REPALphilread/ReP_AL-3D-Lawn-Mower/Mower Arduino Code/Mower_V7.0/Readme.txt

ReP_AL 3D Printed Robot Lawn Mower
----------------------------------

Code V7.0
------------------------------

Upload the MEGA code to the Arduino MEGA
Upload the Nano code to the Arduino Nano
Upload the NodeMCU code to the NodeMCU Board   (includes new code)

Features of 7.0
---------------

- Nearly all of the major Mower settings can now be set using the LCD screen and keypad
- Settings are saved to EEPROM so they are transfered to later code updates.
- Setting Alarms has been improved with an action available for each alarm.
- Fixed the hours and minutes roll over in the alarm setting.
- Fixed errorsa with exiting the settings sub menu.

NodeMCU Board URL:
------------------
Use this URL to add the NodeMCU board 1.0 to the boards menu.

http://arduino.esp8266.com/stable/package_esp8266com_index.json
