REPALphilread/ReP_AL-3D-Lawn-Mower/Mower Arduino Code/Mower_V6.8/Readme.txt

ReP_AL 3D Printed Robot Lawn Mower
----------------------------------

Code V6.8
------------------------------

Upload the MEGA code to the Arduino MEGA
Upload the Nano code to the Arduino Nano
Upload the NodeMCU code to the NodeMCU Board   (includes new code)

Features of 6.8
---------------

- Fixed error in Clock Setting
- Improved the reliability of Compass Home
- Added a test menu to Go Home to test the docking procedure.

NodeMCU Board URL:
http://arduino.esp8266.com/stable/package_esp8266com_index.json
