REPALphilread/ReP_AL-3D-Lawn-Mower/Mower Arduino Code/Mower_V6.6/Readme.txt

ReP_AL 3D Printed Robot Lawn Mower
----------------------------------

Code V6.4
------------------------------

Upload the MEGA code to the Arduino MEGA
Upload the Nano code to the Arduino Nano
Upload the NodeMCU code to the NodeMCU Board

Features of 6.6
---------------

- Spiral cut feature available.  (be careful on slopes)
- More EEPROM settings available
- Improved compass home feature and angle setting

DO NOT USE!!!!

- Tip safety - not working yet
- Parallel cut - not working 100% yet.

NodeMCU Board URL:
http://arduino.esp8266.com/stable/package_esp8266com_index.json
