REPALphilread/ReP_AL-3D-Lawn-Mower/Mower Arduino Code/Mower_V6.2/Readme.txt

ReP_AL 3D Printed Robot Lawn Mower
----------------------------------

Code V6.2   
------------------------------

Upload the MEGA code to the Arduino MEGA
Upload the Nano code to the Arduino Nano (same as 6.1)
Upload the NodeMCU code to the NodeMCU Board (same as 6.1)

Features of 6.2
---------------

- Alarm timer function fixed
- Added more options for timed mow
- Easier menu in code to add custom options
- mower displays the off time in timed mow.

NodeMCU Board URL:
http://arduino.esp8266.com/stable/package_esp8266com_index.json
