REPALphilread/ReP_AL-3D-Lawn-Mower/Mower Arduino Code/Mower_V6.10/Readme.txt

ReP_AL 3D Printed Robot Lawn Mower
----------------------------------

Code V6.1   
------------------------------

Upload the MEGA code to the Arduino MEGA
Upload the Nano code to the Arduino Nano
Upload the NodeMCU code to the NodeMCU Board

Features of 6.1
---------------

- Menu options have been improved. Scrolling in both directions and easier coding.
- More Test options have been added including a compass test and a volt amps test
- First trials at compass mowing (very initial stages - not working well and not advised to use it yet)
- Stabilised the heading hold by using compass degrees instead of heading.

NodeMCU Board URL:
http://arduino.esp8266.com/stable/package_esp8266com_index.json
