REPALphilread/ReP_AL-3D-Lawn-Mower/Mower Arduino Code/Mower_V5.3.2/Readme.txt

ReP_AL 3D Printed Robot Lawn Mower
----------------------------------

Code V5.3.2    - BETA (in  test)
------------------------------

Upload the MEGA code to the Arduino MEGA
Upload the Nano code to the Arduino Nano

Features of 5.2
---------------

- BETA for tracking to home (please test)
  All the charge detection has been moved to the Nano
  Enter the Nano amp limits in the NANO code for your charger to send a charge = 1 signal to the MEGA when the charger is detected.
- Improved the Serial output visual for easier overview of what the mower is doing.
