REPALphilread/ReP_AL-3D-Lawn-Mower/Mower Arduino Code/Mower_V5.8/Readme.txt

ReP_AL 3D Printed Robot Lawn Mower
----------------------------------

Code V5.8    - BETA 
------------------------------

Upload the MEGA code to the Arduino MEGA
Upload the Nano code to the Arduino Nano

Features of 5.8
---------------

- Code layout and logic is changed - I needed to simplify it all to make the WIFI possible in the future
- Test sketches intgrated into the main program.  Choose Tests on the menu options and select the test
- Rain sensor added - turn on and off in the settings
- Improved Serial communication between the NANO and the MEGA.
- Reverse motors option removed. You need to get the cables correct. Its too complicasted to cater for all cabling variations
-
