REPALphilread/ReP_AL-3D-Lawn-Mower/Mower Arduino Code/Mower_V9.2/SDCard BMP/PID.bmp

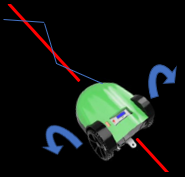
Mower Arduino Code/Mower_V9.2/SDCard BMP/PID.bmp
