REPALphilread/ReP_AL-3D-Lawn-Mower/Metal Parts/STL/Rear Axle - Little Monster.stl

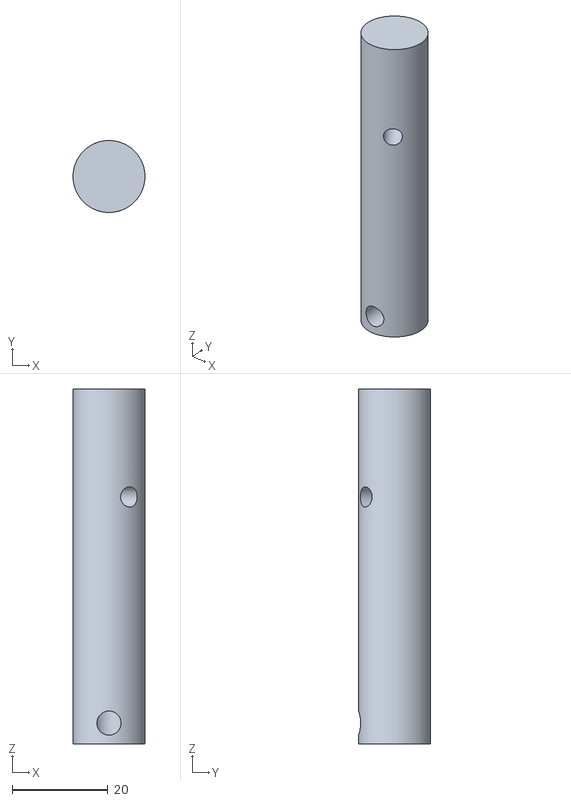
[picture p24: CAD file, 2020-04-30, last stored version]
Metal Parts/STL/Rear Axle - Little Monster.stl
15.0 x 15.0 x 74.0
