REPALphilread/ReP_AL-3D-Lawn-Mower/RTK GPS STL Files/STL RTK Base Station Case/02 Sliding Lid.stl

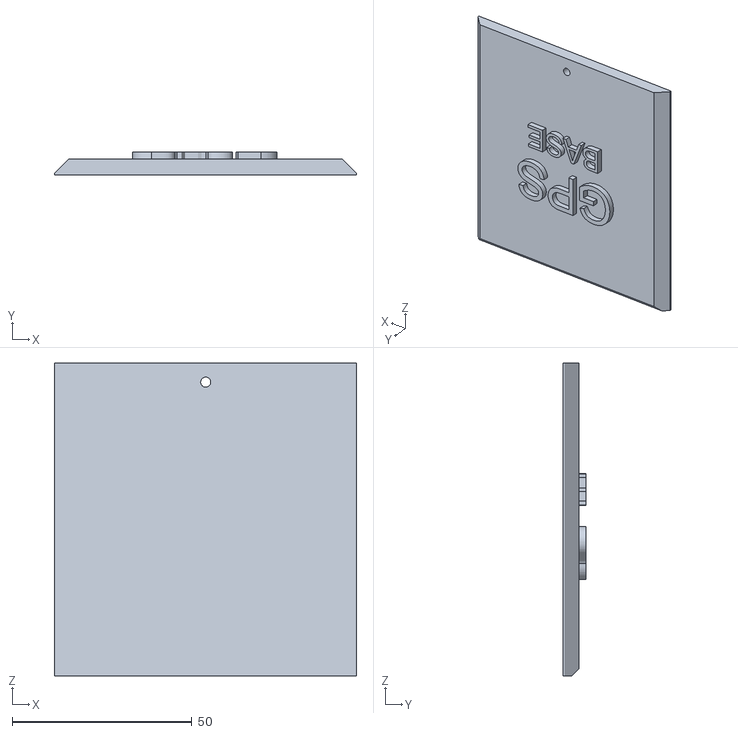
[picture p25: CAD file, 2020-06-30, last stored version]
RTK GPS STL Files/STL RTK Base Station Case/02 Sliding Lid.stl
84.0 x 6.50 x 86.9
