REPALphilread/ReP_AL-3D-Lawn-Mower/RTK GPS STL Files/STL RTK GPS Rover Case/ESP32 Lid.stl

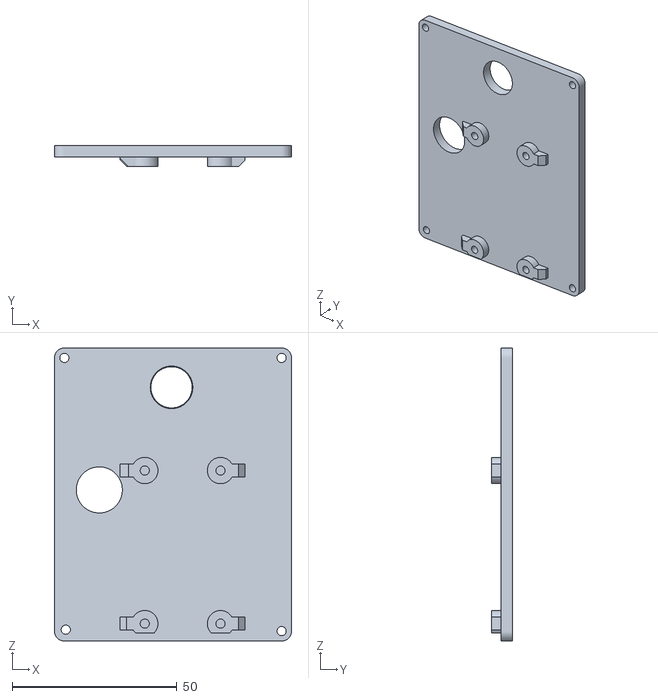
[picture p26: CAD file, 2020-06-30, last stored version]
RTK GPS STL Files/STL RTK GPS Rover Case/ESP32 Lid.stl
72.0 x 6.48 x 89.0
