REPALphilread/ReP_AL-3D-Lawn-Mower/Metal Parts Step Files/Drill Templates/Blade Motor Adapter/Hand Drill/02 Blade Adapter Hand Drill 2.stl

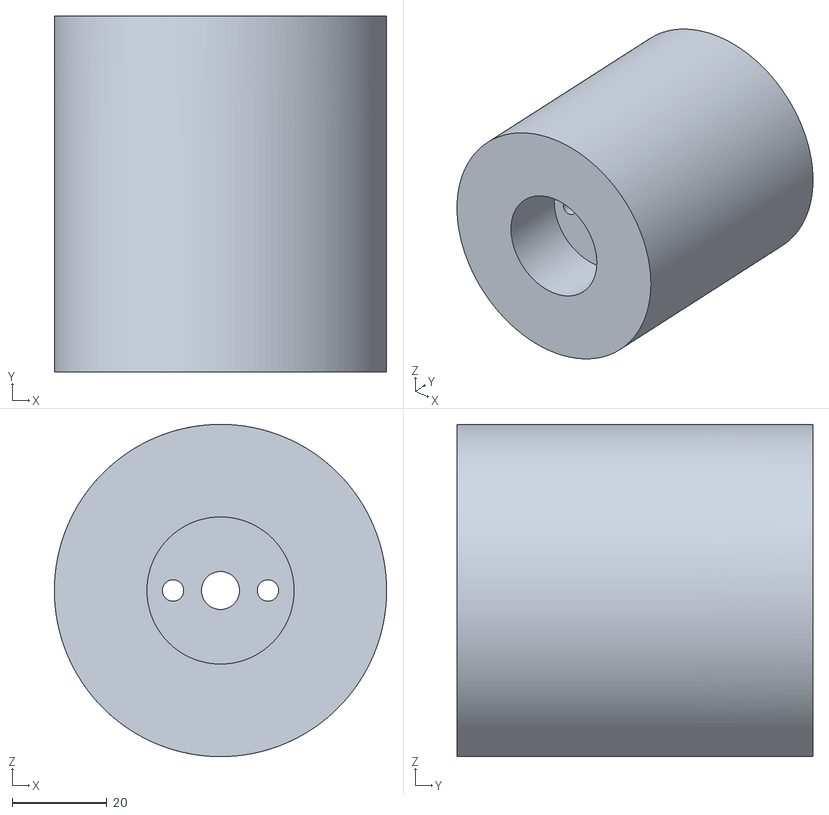
[picture p27: CAD file, 2020-04-07, last stored version]
Metal Parts Step Files/Drill Templates/Blade Motor Adapter/Hand Drill/02 Blade Adapter Hand Drill 2.stl
70.0 x 75.0 x 70.0
