REPALphilread/ReP_AL-3D-Lawn-Mower/Metal Parts Step Files/Drill Templates/Wheel Axle/Drill Press/01 Drill 3mm End Hole Template.stl

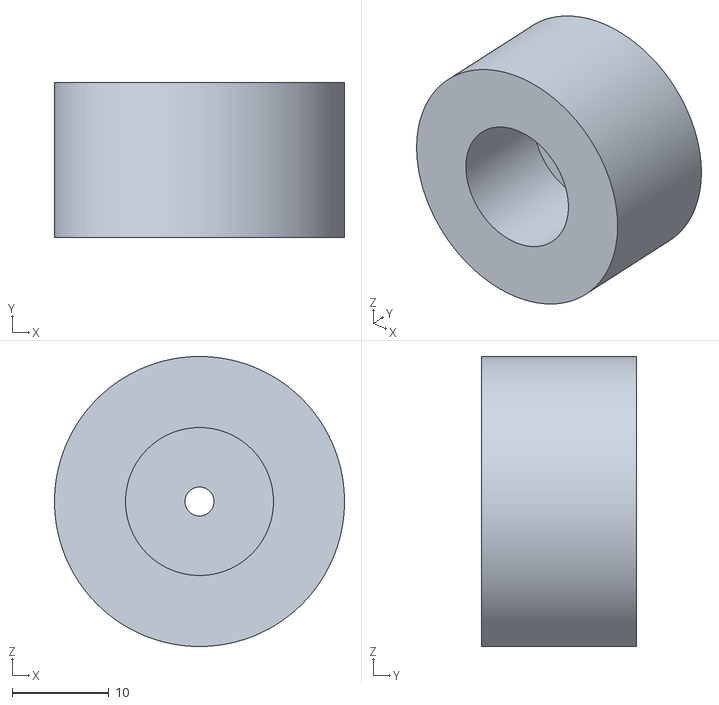
[picture p28: CAD file, 2020-04-07, last stored version]
Metal Parts Step Files/Drill Templates/Wheel Axle/Drill Press/01 Drill 3mm End Hole Template.stl
30.0 x 16.0 x 30.0
