REPALphilread/ReP_AL-3D-Lawn-Mower/Metal Parts Step Files/Drill Templates/Wheel Axle/Hand Drill/02 Drill 6mm End Hole Hand Drill Template.stl

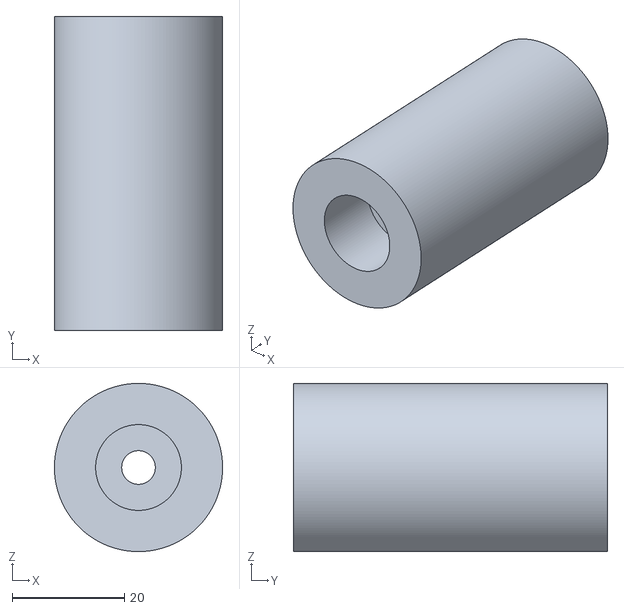
[picture p29: CAD file, 2020-04-07, last stored version]
Metal Parts Step Files/Drill Templates/Wheel Axle/Hand Drill/02 Drill 6mm End Hole Hand Drill Template.stl
30.0 x 56.0 x 30.0
