REPALphilread/ReP_AL-3D-Lawn-Mower/Metal Parts/STL/Mower Disc Adapter.stl

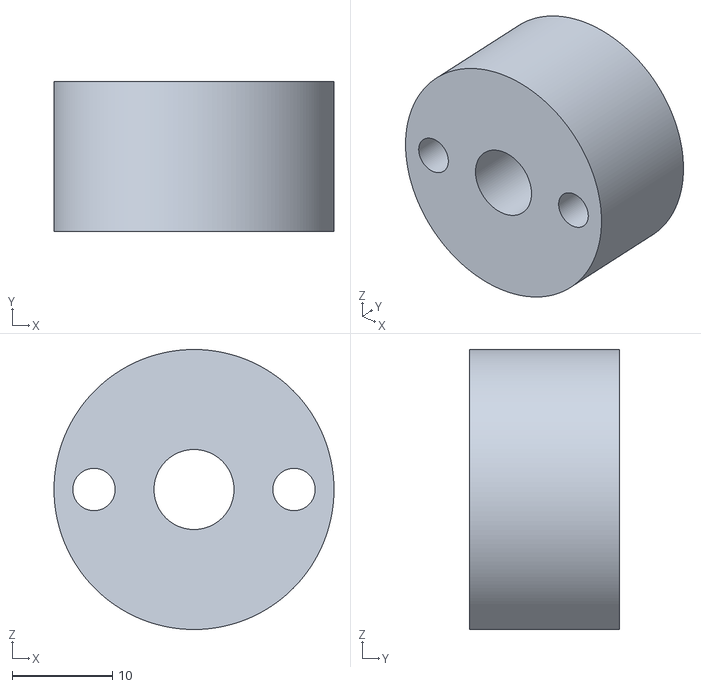
[picture p30: CAD file, 2020-04-30, last stored version]
Metal Parts/STL/Mower Disc Adapter.stl
28.0 x 15.0 x 28.0
