REPALphilread/ReP_AL-3D-Lawn-Mower/RTK GPS STL Files/STL RTK Base Station Case/03 Wire Clamp.stl

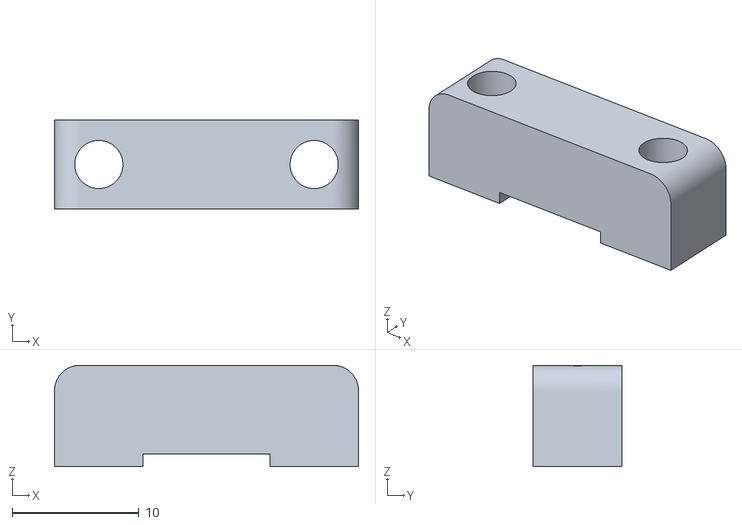
[picture p31: CAD file, 2020-06-30, last stored version]
RTK GPS STL Files/STL RTK Base Station Case/03 Wire Clamp.stl
24.0 x 7.00 x 8.00
