REPALphilread/ReP_AL-3D-Lawn-Mower/Metal Parts/STL/Rear Axle - 330 LAM.stl

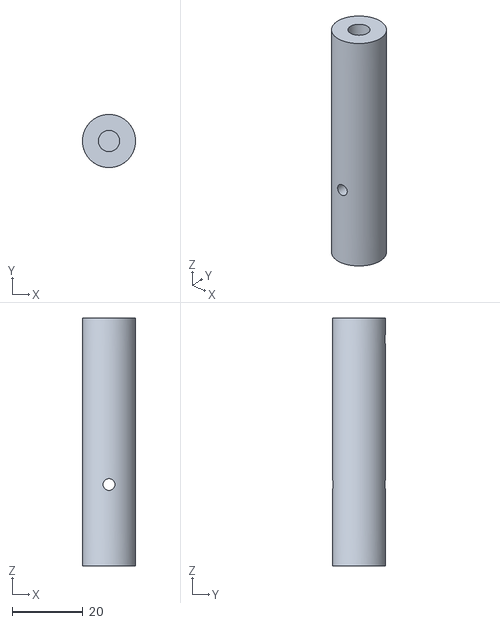
[picture p32: CAD file, 2020-04-30, last stored version]
Metal Parts/STL/Rear Axle - 330 LAM.stl
15.0 x 15.0 x 70.0
