REPALphilread/ReP_AL-3D-Lawn-Mower/Metal Parts Step Files/Drill Templates/95 Drill 5.5mm End Template.stl

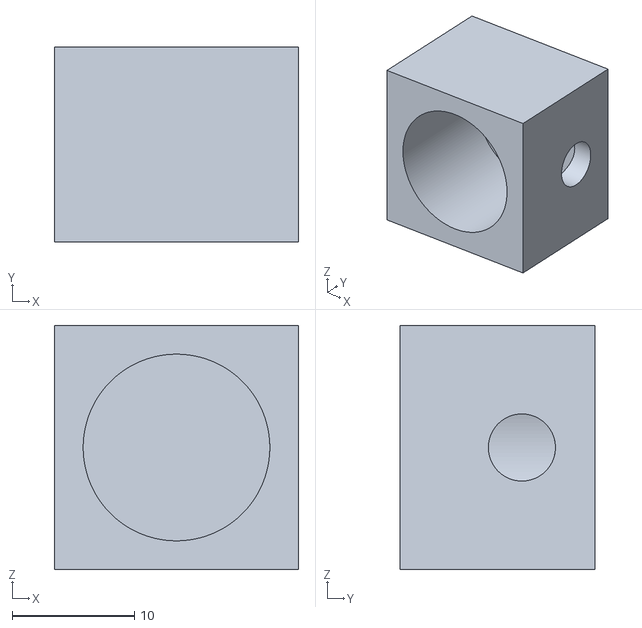
[picture p33: CAD file, 2020-04-07, last stored version]
Metal Parts Step Files/Drill Templates/95 Drill 5.5mm End Template.stl
20.0 x 16.0 x 20.0
