REPALphilread/ReP_AL-3D-Lawn-Mower/Perimeter Wire Transmitter/Sender_Station_V2.ino

/*
  Ardumower (www.ardumower.de)
 Copyright (c) 2013-2014 by Alexander Grau
 Copyright (c) 2013-2014 by Sven Gennat
 Copyright (c) 2015 by Jürgen Lange
 
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
 You should have received a copy of the GNU General Public License
 along with this program.  If not, see <http://www.gnu.org/licenses/>.
 */

/*
  Perimeter sender v2   (for details see   http://wiki.ardumower.de/index.php?title=Perimeter_wire  )  
 Requires: Perimeter sender PCB v1.0   ( https://www.marotronics.de/Perimeter-Sender-Prototyp )
 
 */

#include <EEPROM.h>
#include <RunningMedian.h>
#include <TimerOne.h>




//#define USE_DEVELOPER_TEST    1      // uncomment for new perimeter signal test (developers) 
//---------------------------------------------------------------------------------------------------

#define USE_AUTO_PERIMETER_CURRENT  1 // Use auto Perimeter power set to 0 for not used
// Spannungsmessung
long previousMillisVolt = 0;        // will store last time messure was updated
long intervalVolt = 5;           // voltage messeurement interval (milliseconds)
int counterVolt = 0; // messurement counter for output voltage
int VoltAdc = 0 ; // actual ADC voltage messurement
float Vref = 5.0; // reference Voltage of ADC
float R1 = 100000.0; //value of voltage divider resistor (R1)
float R2 = 10000.0; //value of voltage divider resistor (R2)
float Vdc = 0; // actual messurement voltage in Volt
// Strommessung
long previousMillisAmpere = 0; //Perimeter current last messeurement
long intervalAmpere = 10; // Perimeter current messeurement interval (milliseconds)
int counterAmpere = 0; // messurement counter for Perimeter current average 
float AmpereAdc = 0; // actual ADC messurement for Perimeter current
float AmpereDC = 0; // actual Perimeter current in Ampere
// Leistung
float perimeterPower = 0; // actual Perimeter power in watts
float perimeterMaxPower = 7.00; // (7W) Max Perimeter transmitting power in watts
byte perimeterPowerPWM = 200; // PWM start value
#define pinPerimeterPower  11 // PWM pin for Voltage-Control (11)--->(OPA2340)--->(PIN 4 of LM2596)

byte printTag = 1;                    // Ausgabesteuerung c = calib, 0 = normal, 1 = Regelung
// --- MC33926 motor driver ---
#define USE_DOUBLE_AMPLTIUDE    1         // uncomment to use +/- input voltage for amplitude (default), 
// comment to use only +input/GND voltage for amplitude

#define pinIN1       9  // M1_IN1         (if using old L298N driver, connect this pin to L298N-IN1)
#define pinIN2       2  // M1_IN2         (if using old L298N driver, connect this pin to L298N-IN2)
#define pinPWM       3  // M1_PWM / nD2   (if using old L298N driver, leave open)
#define pinEnable    5  // EN             (connect to motor driver enable)             

// motor driver fault pin
#define pinFault     4  // M1_nSF
#define USE_PERI_FAULT        0     // use pinFault for driver fault detection? (set to '0' if not connected!)

// motor driver feedback pin (=perimeter open/close detection, used for status LED)
#define USE_PERI_CURRENT      0     // use pinFeedback for perimeter current measurements? (set to '0' if not connected!)
#define pinFeedback A0  // M1_FB
#define PERI_CURRENT_MIN    0.03     // minimum Ampere for perimeter-is-closed detection 

// ---- sender current control (via potentiometer) ----
// sender modulates signal (PWM), based on duty-cycle set via this potentiometer
#define USE_POT      0  // use potentiometer for current control? (set to '0' if not connected!)
#define pinPot      A3  // 100k potentiometer (current control)   

// ---- sender automatic standby (via current sensor for charger) ----
// sender detects robot via a charging current through the charging pins
#define USE_CHG_CURRENT       0     // use charging current sensor for robot detection? (set to '0' if not connected!)
#define pinChargeCurrent     A2     // ACS712-05 current sensor OUT
#define CHG_CURRENT_MIN   0.008      // minimum Ampere for charging detection

// ---- sender status LED ----
#define  pinLED 13  // ON: perimeter closed, OFF: perimeter open, BLINK: robot is charging


// code version 
#define VER "592"

// --------------------------------------

volatile int step = 0;
volatile boolean enableSender = true;


double duty = 1.0;    // 100 duty%
int dutyPWM = 0;
double chargeCurrent = 0;
double periCurrentAvg = 0; 
double periCurrentMax = 0; 
int faults = 0;
boolean isCharging = false;
boolean stateLED = false;
unsigned int chargeADCZero = 0;
RunningMedian<unsigned int,16> periCurrentMeasurements;
RunningMedian<unsigned int,96> chargeCurrentMeasurements;

unsigned long nextTimeControl = 0;
unsigned long nextTimeInfo = 0;
unsigned long nextTimeToggleLED = 0;


// must be multiple of 2 !
// http://grauonline.de/alexwww/ardumower/filter/filter.html    
// "pseudonoise4_pw" signal (sender)

#ifdef USE_DEVELOPER_TEST
// a more motor driver friendly signal (sender)
int8_t sigcode[] = {  
  1,0,0,0,0,
  1,0,0,0,0,
  -1,0,0,0,0,
  1,0,0,0,0   };
#else
int8_t sigcode[] = { 
  1,1,-1,-1,1,-1,1,-1,-1,1,-1,1,1,-1,-1,1,-1,-1,1,-1,-1,1,1,-1 };
#endif


// using transparently 5v / 1.1v ref
int analogReadMillivolt(int pin){
  int millivolt;
  int adc;
  // first read using 5v ref 
  adc = analogRead(pin);
  millivolt = ((double)adc) / 1024.0 * 5000.0;  
  // ist so nicht sinnvoll da der ADC Zeit braucht sich umzustellen erste Messung ist ungenau!!
  /* if (adc < 10){
   // read using 1.1v ref
   analogReference(INTERNAL);
   adc = analogRead(pin);
   millivolt = ((double)adc) / 1024.0 * 1100.0;
   analogReference(DEFAULT); 
   }*/
  return millivolt;
}


void timerCallback(){       
  if (enableSender){
    if (sigcode[step] == 1) {      
      digitalWrite(pinIN1, LOW);                           
#ifdef USE_DOUBLE_AMPLTIUDE      
      digitalWrite(pinIN2, HIGH);                                 
#endif             
      digitalWrite(pinEnable, HIGH);
    } 
    else if (sigcode[step] == -1) {              
      digitalWrite(pinIN1, HIGH);          
      digitalWrite(pinIN2, LOW);                                 
      digitalWrite(pinEnable, HIGH);                           
    } 
    else {
      digitalWrite(pinEnable, LOW);
    } 
    step ++;    
    if (step == sizeof sigcode) {      
      step = 0;      
    }    
  } 
  else {
    digitalWrite(pinEnable, LOW);    
  }
}

void readEEPROM(){
  if (EEPROM.read(0) == 43){
    // EEPROM data available
    chargeADCZero = (EEPROM.read(1) << 8) | EEPROM.read(2);
  } 
  else Serial.println("no EEPROM data found, using default calibration (INA169)");
  Serial.print("chargeADCZero=");
  Serial.println(chargeADCZero);  
}


void calibrateChargeCurrentSensor(){
  Serial.println("calibrateChargeCurrentSensor (note: robot must be outside charging station!)");
  RunningMedian<unsigned int,32> measurements;
  for (unsigned int i=0; i < measurements.getSize(); i++) {
    unsigned int m = analogRead(pinChargeCurrent);
    //Serial.println(m);
    measurements.add( m );
    delay(50);
  }
  float v;
  measurements.getAverage(v);  
  chargeADCZero = v;
  EEPROM.write(0, 43);
  EEPROM.write(1, chargeADCZero >> 8);
  EEPROM.write(2, chargeADCZero & 255);  
  Serial.println("calibration done");
  readEEPROM();
} 



void setup() {  
  pinMode(pinIN1, OUTPUT);    
  pinMode(pinIN2, OUTPUT);  
  pinMode(pinEnable, OUTPUT);
  pinMode(pinPWM, OUTPUT);  
  pinMode(pinFeedback, INPUT);    
  pinMode(pinFault, INPUT);      
  pinMode(pinPot, INPUT);      
  pinMode(pinChargeCurrent, INPUT);
  analogWrite(pinPerimeterPower, perimeterPowerPWM);
  // configure ADC reference
  analogReference(DEFAULT); // ADC 5.0v ref    
  //analogReference(INTERNAL); // ADC 1.1v ref       

  // sample rate 9615 Hz (19230,76923076923 / 2 => 9615.38)
  int T = 1000.0*1000.0/ 9615.38;
  Serial.begin(115200);

  Serial.println("START");
  Serial.print("Ardumower Sender ");
  Serial.println(VER);
#ifdef USE_DEVELOPER_TEST
  Serial.println("Warning: USE_DEVELOPER_TEST activated");
#endif
  //Serial.println("press...");
  //Serial.println("  1  for current sensor calibration");  
  //Serial.println();

  readEEPROM();
  Serial.print("T=");
  Serial.println(T);    
  Serial.print("f=");
  Serial.println(1000.0*1000.0/T);    
  Timer1.initialize(T);         // initialize timer1, and set period
  //Timer1.pwm(pinPWM, 256);  
  Timer1.attachInterrupt(timerCallback);  
  //digitalWrite(pinIN1, HIGH);
  //digitalWrite(pinIN2, LOW);  
  //tone(pinPWM, 7800);

  // http://playground.arduino.cc/Main/TimerPWMCheatsheet
  // timer 2 pwm freq 31 khz  
  //cli();
  TCCR2B = TCCR2B & 0b11111000 | 0x01;
  //TIMSK2 |= (1 << OCIE2A);     // Enable Output Compare Match A Interrupt  
  //OCR2A = 255;                 // Set compared value
  //sei();
}

void checkKey(){
  if (Serial.available() > 0) {
    char ch = (char)Serial.read();            
    Serial.print("received key=");
    Serial.println(ch);
    while (Serial.available()) Serial.read();
    switch (ch){
    case 'c': 
      calibrateChargeCurrentSensor();           
      break;
    case '0': 
      printTag = 0;           
      break;
    case '1': 
      printTag = 1;           
      break;
    }
  }             
}

// Interrupt service run when Timer/Counter2 reaches OCR2A
//ISR(TIMER2_COMPA_vect) {
//  if (digitalRead(pinFault) == LOW) fault = true; 
//if (digitalRead(pinPWM) == HIGH) fault = true; 
//fault = true;

void fault(){
  Serial.println("MC_FAULT");
  for (int i=0; i < 10; i++){
    digitalWrite(pinLED, HIGH);
    delay(50);
    digitalWrite(pinLED, LOW);
    delay(50);
  }  
  faults++;                          
}


void loop()
{
  //---------------------------------------------------------------------------------------------------
  if(USE_AUTO_PERIMETER_CURRENT)
  {
    unsigned long currentMillis = millis(); // save actual moment

    // -----------------------------------------------------------------------------------------
    //                   Messurement of Voltage and Calculate Perimeter-Power
    // -----------------------------------------------------------------------------------------
    if(currentMillis - previousMillisVolt > intervalVolt) // check messurement interval
    {
      previousMillisVolt = currentMillis; // save the last time of messurement  

      if (counterVolt < 49) // check average messurement Volt-counter
      {
        counterVolt ++; // add counter +1
        VoltAdc = VoltAdc + analogRead(A3); // add actual messurement to previous messurement
      } 
      else 
      {
        VoltAdc = VoltAdc / 50; // calculate average voltage
        Vdc = (VoltAdc*5.0)/1024; // calculate real voltage
        Vdc=(Vdc*((R1+R2)/R2))+0.3; // (+0.3) = correction factor over all
        perimeterPower = Vdc * AmpereDC; // calculate Perimeter-Power
        counterVolt = 0; // set counter to 0 for next messurement
        // **** Control Perimeter-Power adjust DC/DC converter voltage over PWM ****
        // step output voltage down
        if(perimeterPower > perimeterMaxPower && perimeterPowerPWM < 255) perimeterPowerPWM ++;
        // step output voltage up
        if(perimeterPower < perimeterMaxPower && perimeterPowerPWM > 1) perimeterPowerPWM --;
        analogWrite(pinPerimeterPower, perimeterPowerPWM); // set new PWM value for output
      }
    }
    // -----------------------------------------------------------------------------------------
    //                          Messurement of Current for Perimeter-Power
    // -----------------------------------------------------------------------------------------
    if(currentMillis - previousMillisAmpere > intervalAmpere) // check messurement interval 
    {
      previousMillisAmpere = currentMillis; // save the last time of messurement   

      if (counterAmpere < 19) // check average messurement Current-counter
      {
        counterAmpere ++; // add counter +1
        AmpereAdc = AmpereAdc + analogRead(A7); // add actual messurement to previous messurement
      } 
      else 
      {
        AmpereAdc = AmpereAdc / 20; // calculate average current
        AmpereDC = AmpereAdc*Vref/1023*0.5; // calculate real current
        counterAmpere = 0;  // set counter to 0 for next messurement
      }
    }
    // -----------------------------------------------------------------------------------------
    // -----------------------------------------------------------------------------------------
  } // <------------- END if(USE_AUTO_PERIMETER_CURRENT)
  // -------------------------------------------------------------------------------------------
  // -------------------------------------------------------------------------------------------
  // -------------------------------------------------------------------------------------------
  if (millis() >= nextTimeControl){                    
    nextTimeControl = millis() + 100;
    dutyPWM = ((int)(duty * 255.0));
    if (isCharging){
      // switch off perimeter 
      enableSender = false;
    } 
    else {
      // switch on perimeter
      enableSender = true;
      //analogWrite(pinPWM, 255);
      analogWrite(pinPWM, dutyPWM);
      if ( USE_PERI_FAULT && (dutyPWM == 255) && (digitalRead(pinFault) == LOW) ) {
        enableSender = false;
        dutyPWM = 0;
        analogWrite(pinPWM, dutyPWM);
        fault();    
      }    
    }
  }

  if (millis() >= nextTimeInfo){                
    nextTimeInfo = millis() + 500;                
    checkKey();        

    //unsigned int v = 0;
    float v = 0;
    // determine charging current (Ampere)        
    if (USE_CHG_CURRENT) {                
      chargeCurrentMeasurements.getAverage(v);        
      chargeCurrent = ((double)(((int)v)  - ((int)chargeADCZero))) / 1023.0 * 1.1;  
      isCharging = (abs(chargeCurrent) >= CHG_CURRENT_MIN); 
    }  

    if (USE_PERI_CURRENT) {
      // determine perimeter current (Ampere)
      periCurrentMeasurements.getAverage(v);    
      periCurrentAvg = ((double)v) / 1023.0 * 1.1 / 0.525;   // 525 mV per amp    
      unsigned int h;
      periCurrentMeasurements.getHighest(h);    
      periCurrentMax = ((double)h) / 1023.0 * 1.1 / 0.525;   // 525 mV per amp    
    }

    if(printTag == 0)
    {
      Serial.print("time=");
      Serial.print(millis()/1000);    
      Serial.print("\tchgCurrent=");
      Serial.print(chargeCurrent, 3);
      Serial.print("\tchgCurrentADC=");
      chargeCurrentMeasurements.getAverage(v);        
      Serial.print( v );       
      Serial.print("\tisCharging=");
      Serial.print(isCharging);    
      Serial.print("\tperiCurrent avg=");
      Serial.print(periCurrentAvg);
      Serial.print("\tmax=");
      Serial.print(periCurrentMax);
      Serial.print("\tduty=");
      Serial.print(duty);
      Serial.print("\tdutyPWM=");        
      Serial.print(dutyPWM);        
      Serial.print("\tfaults=");
      Serial.print(faults);       
      Serial.println();
    }

    if(printTag == 1)
    {
      Serial.print("V-OUT= ");
      Serial.print(Vdc);    
      Serial.print("  A-OUT= ");
      Serial.print(AmpereDC, 2);
      Serial.print("  P-OUT-MAX= ");
      Serial.print(perimeterMaxPower);
      Serial.print("  P-OUT= ");
      Serial.print(perimeterPower, 2);
      Serial.print("  PWM-OUT= ");
      Serial.print(perimeterPowerPWM);
      Serial.println();
    }

    if (USE_POT){
      // read potentiometer
      duty = max(0.01, ((float)map(analogRead(pinPot),  0,1023,   0,1000))  /1000.0 );
    }              
  }

  if (USE_PERI_CURRENT) {
    periCurrentMeasurements.add( analogRead(pinFeedback) );    
  }

  if (USE_CHG_CURRENT){
    // determine charging current (Ampere)         
    chargeCurrentMeasurements.add( analogRead( pinChargeCurrent) );
  }

  // LED status 
  if (isCharging) {    
    // charging
    if (millis() >= nextTimeToggleLED){
      nextTimeToggleLED = millis() + 500;
      stateLED = !stateLED;
    }
  } 
  else {
    // not charging => indicate perimeter wire state (OFF=broken)
    stateLED = (periCurrentAvg >= PERI_CURRENT_MIN);
  }
  digitalWrite(pinLED, stateLED);   


}
