REPALphilread/ReP_AL-3D-Lawn-Mower/Mower Arduino Code/Mower_V9.2/NODEMCU_V9.2/NODEMCU_V9.2.ino

/* Comment this out to disable prints and save space */
#define BLYNK_PRINT Serial
#include <ESP8266WiFi.h>
#include <BlynkSimpleEsp8266.h>
#include <SoftwareSerial.h>

SoftwareSerial NodeMCU(D2,D3);   //RXD2 TXD3

//#define LED LED_BUILTIN

#define LED D4      // on various NODEMCU boards the LED Pin is different.....

// You should get Auth Token in the Blynk App.
// Go to the Project Settings (nut icon).

char auth[] = "Blynk Token Number";


// Your WiFi credentials.
// Set password to "" for open networks.
char ssid[] = "WIFI NAME";
char pass[] = "WIFI Password";


int buttonState = 0;
char  Version[16];

// RX Variables
float val_VoltNow;                  // Battery Voltage from MEGA
float BatteryVoltage;               // Voltage read last RX
int Loop_Cycle_Mowing;              // Current Loop Cycle from MEGA

int Mower_Parked;
int Mower_Parked_Low_Batt;
int Mower_Docked;
int Mower_Docked_Filter;
int Mower_Running;
int Mower_Running_Filter;
int Mower_Lost;
int Charge_Detected;
int Tracking_Wire;
int Compass_Heading_Lock;

int Compass_Activate;
int Compass_Heading_Hold_Enabled;
int GYRO_Enabled;

int Sonar_1_Activate;
int Sonar_2_Activate;
int Sonar_3_Activate;
int Bumper_Activate_Frnt;

int i;                              // Transmit blank code

bool Mower_Already_Started = 0;
bool Going_Home_Already = 0;

int j;
int k;
int transmit_blynk_code = 0;

bool Manuel_Mode;
int Automatic_Mode;


int loopstatus = 0;
int All;
int RX_Data_Recieved;
int lastConnectionAttempt = millis();
int connectionDelay = 5000; // try to reconnect every 5 seconds

// MEGA Check
int Loop_Cycle_Mowing_Check_1;
int Loop_Cycle_Mowing_Check_2;
float val_VoltNow_Check_1;
float val_VoltNow_Check_2;
int Check_MEGA = 0;
int Error_Loop;
int Error_Volt;
int Total_Error;
int Max_Error = 40;
bool MEGA_Watch_Enabled = 1;

BlynkTimer timer;
WidgetLCD lcd(V6);


// This function sends Arduino's up time every second to Virtual Pin (5).
// In the app, Widget's reading frequency should be set to PUSH. This means
// that you define how often to send data to Blynk App.

void myTimerEvent()  {
  if (  (BatteryVoltage > 10) && (BatteryVoltage < 15) ){
      Blynk.virtualWrite(V3, BatteryVoltage);
  }

  Blynk.virtualWrite(V5, Loop_Cycle_Mowing);


}

void setup()
{
  Serial.begin(9600);
  NodeMCU.begin(9600);
  Serial.println();
  Serial.println("Setting up NODEMCU........");
  Serial.println("");
  pinMode(D2,INPUT);
  pinMode(D3,OUTPUT);
  pinMode(D5,OUTPUT);
  pinMode(D6,OUTPUT);
  digitalWrite(D5, HIGH);
  digitalWrite(LED, HIGH);                          // Turn off LED Light
  WIFI_Connect();                                   // Connect to the WIFI
  Clear_APP();
  lcd.clear();
  pinMode(LED, OUTPUT);


}



//Functions
//***********************************


void WIFI_Connect() {
  
  int mytimeout = millis() / 1000;
  Serial.println();
  Serial.println("*********************************************");
  Blynk.begin(auth, ssid, pass);
  
  
  while (Blynk.connected() != WL_CONNECTED) {
    delay(500);
      if((millis() / 1000) > mytimeout + 3){                      // try for less than 4 seconds to connect to WiFi router
      break;
    }
  }
  
  if(!Blynk.connected()) {
    digitalWrite(LED, HIGH);
    Serial.println("NODEMCU Disconnected");
    Serial.println("Reconnecting . . . . . . ");
    WIFI_Connect();

    }
  else {
    digitalWrite(LED, LOW);
    Serial.println("Connected. . . . . .");
    // Setup a function to be called every second
    timer.setInterval(1000L, myTimerEvent);
    }
  }







void loop()  {

  loopstatus = loopstatus + 1 ;
  RX_Data_Recieved = 0;                         // resets the data received bool 
  
  if(!Blynk.connected()) {
    Blynk.run();
    timer.run();  
    digitalWrite(LED, HIGH);
    Serial.println("------------------------");
    Serial.println("NODEMCU Disconnected");
    Serial.println("Reconnecting ... ");
    WIFI_Connect() ;
    }
  else {
    Blynk.run();
    timer.run();  
    digitalWrite(LED, LOW);         //LED is inverted on a MODEMCU...        
    Receive_All_From_MEGA();
    Update_Blynk_App_With_Status();
    if (MEGA_Watch_Enabled == 1) Check_MEGA_Status();
    Serial.println("");     // new line serial monitor
  }


}
