REPALphilread/ReP_AL-3D-Lawn-Mower/Mower Arduino Code/Mower_V9.2/TFT_V2.3/Menu_AlarmX.ino

void Print_AlarmX_Menu() {  

     // Framework for the buttons - setting the start position of the Quick start button wil automatically then space the other buttons
    tft.fillScreen(BLACK);
    int Label_Time_Spacing = 30;          // Space between the text and the -ve button
    int Button_W = 50;                // width of the button
    int Button_H = 40;                // height of the button
    int Button_Spacing = 5;           // Space between the -ve and +ve buttons
    int Time_Spacing = 150;            // Distance between the Hours and Minutes Number
    Offset_Btn = 25;
    int Time_Button_Spacing = 100;

    // Main Menu Title

    tft.setTextSize(2); 
    tft.setTextColor(GREEN, BLACK);      //Text Colour/ Background Colour
    tft.setCursor(10, 10);            // Text Coordinates X, Y
    if (Alarm_X_Selected == 1) tft.print(F("Alarm 1 Settings"));  
    if (Alarm_X_Selected == 2) tft.print(F("Alarm 2 Settings"));  
    if (Alarm_X_Selected == 3) tft.print(F("Alarm 3 Settings"));  
    
    // Framework for the + - buttons - setting the start position of the + button wil automatically then space the - button

    // Top left position of the first menu item.    
    Pos_X1   = 35;
    Pos_Y1   = 50;

    
    // Size of the Alarm Time Label
    tft.setTextSize(2); 
    tft.setTextColor(YELLOW, BLACK);      //Text Colour/ Background Colour
    tft.setCursor(Pos_X1, Pos_Y1);            // Text Coordinates X, Y
    tft.print(F("Start Time"));  

    // Size of the Alarm Time Numbers
    tft.setTextSize(9); 
    tft.setTextColor(RED, BLACK);      //Text Colour/ Background Colour

    // Hours X 10 
    Pos_X1 = Pos_X1;
    Pos_Y1 = Pos_Y1 + Label_Time_Spacing;  
    tft.setCursor(Pos_X1, Pos_Y1);            // Text Coordinates X, Y
        if (Alarm_X_Hour > 9) tft.print(Alarm_X_Hour);
        if (Alarm_X_Hour < 10) {
          tft.print("0");
          tft.print(Alarm_X_Hour);
        }

    Pos_X3 = Pos_X1 + 100;
    Pos_Y3 = Pos_Y1;  
    tft.setCursor(Pos_X3, Pos_Y3);            // Text Coordinates X, Y
    tft.print(F(":"));     


    // Minutes X 10 
    Pos_X2 = Pos_X1 + Time_Spacing;
    Pos_Y2 = Pos_Y1;  
    tft.setCursor(Pos_X2, Pos_Y2);            // Text Coordinates X, Y
        if (Alarm_X_Minute > 9) tft.print(Alarm_X_Minute);
        if (Alarm_X_Minute < 10) {
          tft.print("0");
          tft.print(Alarm_X_Minute);
        }
    
    // + - Hour Value
    int Button_X = Pos_X1 + (0.5 * Button_W);
    int Button_Y = Pos_Y1 + Time_Button_Spacing;
 
    UP1_BTN.initButton(&tft, Button_X, Button_Y, Button_W, Button_H, WHITE, CYAN, BLACK, "+", 2);
    DOWN1_BTN.initButton(&tft, (Button_X + (Button_W + Button_Spacing)), Button_Y, Button_W, Button_H, WHITE, CYAN, BLACK, "-", 2);

    UP1_BTN.drawButton(false);
    DOWN1_BTN.drawButton(false);

    // + - Minute Value
    Button_X = Pos_X2 + (0.5 * Button_W);
    Button_Y = Pos_Y2 + Time_Button_Spacing;
 
    UP2_BTN.initButton(&tft, Button_X, Button_Y, Button_W, Button_H, WHITE, CYAN, BLACK, "+", 2);
    DOWN2_BTN.initButton(&tft, (Button_X + (Button_W + Button_Spacing)), Button_Y, Button_W, Button_H, WHITE, CYAN, BLACK, "-", 2);

    UP2_BTN.drawButton(false);
    DOWN2_BTN.drawButton(false);


    // Position Action Label
    tft.setTextSize(2); 
    tft.setTextColor(YELLOW, BLACK);      //Text Colour/ Background Colour
    tft.setCursor(Pos_X1, Pos_Y1 + 150);            // Text Coordinates X, Y
    tft.print(F("Action")); 

    // Action

    Button_W = 260;
    Button_X = Pos_X1 + (0.5 * Button_W);
    Button_Y = Pos_Y1 + Time_Button_Spacing + 100;
 
    if (Alarm_X_Action == 1) UP3_BTN.initButton(&tft, Button_X, Button_Y, Button_W, Button_H, WHITE, BLUE, WHITE, "Exit Z1", 2);
    if (Alarm_X_Action == 2) UP3_BTN.initButton(&tft, Button_X, Button_Y, Button_W, Button_H, WHITE, MAGENTA, WHITE, "Exit Z2", 2);
    if (Alarm_X_Action == 3) UP3_BTN.initButton(&tft, Button_X, Button_Y, Button_W, Button_H, WHITE, YELLOW, BLACK, "Mow Line", 2);
    if (Alarm_X_Action == 4) UP3_BTN.initButton(&tft, Button_X, Button_Y, Button_W, Button_H, WHITE, WHITE, BLACK, "Quick Go", 2);
    if (Alarm_X_Action == 5) UP3_BTN.initButton(&tft, Button_X, Button_Y, Button_W, Button_H, WHITE, GREY, BLACK, "Custom", 2);
    UP3_BTN.drawButton(false);


    // ALARM ON/OFF

    Button_W = 100;
    Button_H = 120;
    Pos_X4 = 380;
    Pos_Y4 = Pos_Y1 + (0.5* Button_H);
    Button_X = Pos_X4;
    Button_Y = Pos_Y4;
 
    if (Alarm_X_ON == 0) UP4_BTN.initButton(&tft, Button_X, Button_Y, Button_W, Button_H, WHITE, RED, WHITE, "OFF", 2);
    if (Alarm_X_ON == 1) UP4_BTN.initButton(&tft, Button_X, Button_Y, Button_W, Button_H, WHITE, GREEN, BLACK, "ON", 2);
    UP4_BTN.drawButton(false);


// Done Button

    SAVE4_BTN.initButton(&tft, 410, 275, 80, 40, WHITE, CYAN, BLACK, "Save", 2);
    SAVE4_BTN.drawButton(false);


}



void React_to_Button_AlarmX() {

  //If the Button 1 Turn Angle Max is pressed (up or down)
   if ((UP1_BTN.justPressed() )  || (DOWN1_BTN.justPressed())) {
        Value_All = Alarm_X_Hour;
        Label_X = Pos_X1;
        Label_Y = Pos_Y1;
    
    // Actions if UP is pressed
    if (UP1_BTN.justPressed()) {
        Clear_Old_Value_Time();       
        UP1_BTN.drawButton(true);
        Value_All = Value_All + 1;
        if (Value_All > 24) Value_All = 0;
        Alarm_X_Hour = Value_All;
        Print_New_Value_Time();
        }


    // Action if down is pressed
    if (DOWN1_BTN.justPressed()) {
        Clear_Old_Value_Time();
        DOWN1_BTN.drawButton(true);
        Value_All = Value_All - 1;
        if (Value_All < 0) Value_All = 23;
        Alarm_X_Hour = Value_All;
        Print_New_Value_Time();
        }
    
    }

  //If the Reverse Button 2 is pressed (up or down)
   if ((UP2_BTN.justPressed() )  || (DOWN2_BTN.justPressed())) {
        Value_All = Alarm_X_Minute;
        Label_X   = Pos_X2;
        Label_Y   = Pos_Y2;
    
    // Actions if UP is pressed
    if (UP2_BTN.justPressed()) {
        Clear_Old_Value_Time();       
        UP2_BTN.drawButton(true);
        Value_All = Value_All + 1;
        if (Value_All > 59) Value_All = 0;
        Alarm_X_Minute = Value_All;
        Print_New_Value_Time();
        }


    // Action if down is pressed
    if (DOWN2_BTN.justPressed()) {
        Clear_Old_Value_Time();
        DOWN2_BTN.drawButton(true);
        Value_All = Value_All - 1;
        if (Value_All < 0) Value_All = 59;
        Alarm_X_Minute = Value_All;
        Print_New_Value_Time();
        }
    
    }



  //Action Selection
   if (UP3_BTN.justPressed() ) {

        Alarm_X_Action = Alarm_X_Action + 1;
        if (Alarm_X_Action > 5) Alarm_X_Action = 1;
        int Button_W = 260;
        int Button_X = Pos_X1 + (0.5 * Button_W);
        int Button_Y = Pos_Y1 + 200;
        int Button_H = 40; 

 
    if (Alarm_X_Action == 1) UP3_BTN.initButton(&tft, Button_X, Button_Y, Button_W, Button_H, WHITE, BLUE, WHITE, "Exit Z1", 2);
    if (Alarm_X_Action == 2) UP3_BTN.initButton(&tft, Button_X, Button_Y, Button_W, Button_H, WHITE, MAGENTA, WHITE, "Exit Z2", 2);
    if (Alarm_X_Action == 3) UP3_BTN.initButton(&tft, Button_X, Button_Y, Button_W, Button_H, WHITE, YELLOW, BLACK, "Mow Line", 2);
    if (Alarm_X_Action == 4) UP3_BTN.initButton(&tft, Button_X, Button_Y, Button_W, Button_H, WHITE, WHITE, BLACK, "Quick Go", 2);
    if (Alarm_X_Action == 5) UP3_BTN.initButton(&tft, Button_X, Button_Y, Button_W, Button_H, WHITE, GREY, BLACK, "Custom", 2);
       UP3_BTN.drawButton(false);
        
 delay(200);
    
   }

  //Alarm ON/OFF
   if (UP4_BTN.justPressed() ) {

        int Button_W = 100;
        int Button_H = 120;
        Pos_X4 = 380;
        Pos_Y4 = Pos_Y1 + (0.5* Button_H);
        int Button_X = Pos_X4;
        int Button_Y = Pos_Y4;
        bool Changed = 0;

        if ((Alarm_X_ON == 1) && (Changed ==0))  {
          Alarm_X_ON = 0;
          Changed = 1;
          UP4_BTN.initButton(&tft, Button_X, Button_Y, Button_W, Button_H, WHITE, RED, WHITE, "OFF", 2);
          UP4_BTN.drawButton(false);
          }
        
        if ((Alarm_X_ON == 0) && (Changed ==0)) {
          Alarm_X_ON = 1;
          Changed = 1;            
          UP4_BTN.initButton(&tft, Button_X, Button_Y, Button_W, Button_H, WHITE, GREEN, BLACK, "ON", 2);
          UP4_BTN.drawButton(false);
        }

  delay(200);

    
   }


 // Action if Sonar Save is pressed
 if (SAVE4_BTN.justPressed()) {
         Menu_Complete_AlarmX = true;
         tft.fillScreen(BLACK);
         Serial.println(F("Alarm Data Saved and TX"));
         if (Alarm_X_Selected == 1) {
           Alarm_1_ON =     Alarm_X_ON;                 
           Alarm_1_Hour =   Alarm_X_Hour;               
           Alarm_1_Minute = Alarm_X_Minute;             
           Alarm_1_Repeat = Alarm_X_Repeat;                
           Alarm_1_Action = Alarm_X_Action;
           Menu_Active = 920;
           Send_Menu_Selected_To_Mower_MEGA();
           Transmit_Save_Alarm1_Values();
           }
         if (Alarm_X_Selected == 2) {
           Alarm_2_ON =     Alarm_X_ON;                 
           Alarm_2_Hour =   Alarm_X_Hour;               
           Alarm_2_Minute = Alarm_X_Minute;             
           Alarm_2_Repeat = Alarm_X_Repeat;                
           Alarm_2_Action = Alarm_X_Action;
           Menu_Active = 921;
           Send_Menu_Selected_To_Mower_MEGA();
           Transmit_Save_Alarm2_Values();
           }
         if (Alarm_X_Selected == 3) {
           Alarm_3_ON =     Alarm_X_ON;                 
           Alarm_3_Hour =   Alarm_X_Hour;               
           Alarm_3_Minute = Alarm_X_Minute;             
           Alarm_3_Repeat = Alarm_X_Repeat;                
           Alarm_3_Action = Alarm_X_Action;
           Menu_Active = 922;
           Send_Menu_Selected_To_Mower_MEGA();
           Transmit_Save_Alarm3_Values();
           }         
         
         Print_Time_Menu();
         
         }

}


void Clear_Old_Value_Time() {
        // Draws over the previous Value in Black text to clear it.... !?
        tft.setTextSize(9); 
        tft.setTextColor(BLACK, BLACK);      //Text Colour/ Background Colour
        tft.setCursor(Label_X, Label_Y);            // Text Coordinates X, Y
        if (Value_All > 9) tft.print(Value_All);
        if (Value_All < 10) {
          tft.print("0");
          tft.print(Value_All);
        }
        }


void Print_New_Value_Time() {        

        tft.setTextSize(9); 
        tft.setTextColor(RED, BLACK);      //Text Colour/ Background Colour
        tft.setCursor(Label_X, Label_Y);            // Text Coordinates X, Y
        if (Value_All > 9) tft.print(Value_All);
        if (Value_All < 10) {
          tft.print("0");
          tft.print(Value_All);
        }
        }




void Sense_Button_AlarmX() {
    down = Touch_getXY();
    UP1_BTN.press             (down && UP1_BTN.contains(pixel_x, pixel_y));
    DOWN1_BTN.press           (down && DOWN1_BTN.contains(pixel_x, pixel_y));
    UP2_BTN.press             (down && UP2_BTN.contains(pixel_x, pixel_y));
    DOWN2_BTN.press           (down && DOWN2_BTN.contains(pixel_x, pixel_y));
    UP3_BTN.press             (down && UP3_BTN.contains(pixel_x, pixel_y));
    DOWN3_BTN.press           (down && DOWN3_BTN.contains(pixel_x, pixel_y));
    UP4_BTN.press             (down && UP4_BTN.contains(pixel_x, pixel_y));
    SAVE4_BTN.press     (down && SAVE4_BTN.contains(pixel_x, pixel_y));


    if (UP1_BTN.justReleased())             UP1_BTN.drawButton();
    if (DOWN1_BTN.justReleased())           DOWN1_BTN.drawButton();
    if (UP2_BTN.justReleased())             UP2_BTN.drawButton();  
    if (DOWN2_BTN.justReleased())           DOWN2_BTN.drawButton();
    if (UP3_BTN.justReleased())             UP3_BTN.drawButton();
    if (UP4_BTN.justReleased())             UP4_BTN.drawButton();
    if (DOWN3_BTN.justReleased())           DOWN3_BTN.drawButton();
    if (SAVE4_BTN.justReleased())     SAVE4_BTN.drawButton();
    }


void Check_For_Active_Alarms() {
    if ((Alarm_1_ON == 1) || (Alarm_2_ON == 1) || (Alarm_3_ON == 1)) {
      bmpDraw("Alarmbell.bmp", 390, 235);
      if (Alarm_1_ON == 1) Serial.println(F("ALARM 1 ON"));
      if (Alarm_2_ON == 1) Serial.println(F("ALARM 2 ON"));
      if (Alarm_3_ON == 1) Serial.println(F("ALARM 3 ON"));
   
    }
}
