REPALphilread/ReP_AL-3D-Lawn-Mower/Mower Arduino Code/Mower_V9.2/MEGA_V9.2/TFT_TX.ino

// Transmits 7 Data Values to the TFT MEGA on Serial3 Com Port.
// The data values are declared below for the different Menu
// Commands.  This standardises the data transfer method for all
// functions.
//
// Values are transfered from the Mower MEGA to the TFT MEGA for editing in
// the TFT GUI.  The values are then sent back and stored to DueFlash on the MOWER
// MEGA so the mower can carry out the instructions according to the user settings


void TX_7_Data_Values() {
      Serial.println("Sending Data Sets");
      delay(200); 
      Serial3.print(Data1);
      Serial3.println("\a");
      delay(200);  
      Serial3.print(Data2);
      Serial3.println("\b");
      delay(200);  
      Serial3.print(Data3);
      Serial3.println("\c");
      delay(200);  
      Serial3.print(Data4);
      Serial3.println("\d");
      delay(200);
      Serial3.print(Data5);
      Serial3.println("\e");
      delay(200);
      Serial3.print(Data6);
      Serial3.println("\f");
      delay(200);
      Serial3.print(Data7);
      Serial3.println("\g");
      delay(200);
      
      Serial.print(F("Data1:"));
      Serial.println(Data1);
      Serial.print(F("Data2:"));
      Serial.println(Data2);
      Serial.print(F("Data3:"));
      Serial.println(Data3);  
      Serial.print(F("Data4:"));
      Serial.println(Data4);
      Serial.print(F("Data5:"));
      Serial.println(Data5);
      Serial.print(F("Data6:"));
      Serial.println(Data6);
      Serial.print(F("Data7:"));
      Serial.println(Data7);    
      }


void Send_Data_To_TFT() {
    // Depending on the code received the following data set is sent through the Serial 3 port.
    
    // Menu Sonar
    if (TFT_Menu_Command == 10) {
      Serial.println("TX Sonar to TFT");
      Data1 = Sonar_1_Activate;
      Data2 = Sonar_2_Activate;
      Data3 = Sonar_3_Activate;
      Data4 = maxdistancesonar;
      Data5 = Max_Sonar_Hit;
      Data6 = 0;
      Data7 = 0;
      TX_7_Data_Values();

      Serial.print(F("S1 ON = "));
      Serial.println(Sonar_1_Activate);
      Serial.print(F("S2 ON = "));
      Serial.println(Sonar_2_Activate);
      Serial.print(F("S3 ON = "));
      Serial.println(Sonar_3_Activate);
      Serial.print(F("Sonar Max Distance = "));
      Serial.println(maxdistancesonar);
      Serial.print(F("Sonar Sensitivity = "));
      Serial.println(Max_Sonar_Hit);
      Serial.println(F(" "));
      }

    
// 11 is sometimes read if a serial port miscommunication occurs therefore this
// number is not used to start communication from the MEGA:
    if (TFT_Menu_Command == 11) {
      Serial.println("False Command");      
      }


// Navigation Menu is selected on the TFT
    if (TFT_Menu_Command == 9) {
      Serial.println("TX Nav to TFT");
      
      Serial3.print(GPS_Enabled);
      Serial3.println("\a");
      delay(200);  

      Serial.print(F("GPS Enabled = "));
      Serial.println(GPS_Enabled);   
      }


// Battery Menu is selected on the TFT
    if (TFT_Menu_Command == 26) {
      Serial.println("TX Battery to TFT");
      float Temp = Battery_Min * 10;          // Create Temp float value to transfer the decimal to the int
      int Temp2 = Temp;
      Data1 = Temp2;
      Data2 = Low_Battery_Instances_Chg;
      Data3 = 0;
      Data4 = 0;
      Data5 = 0;
      Data6 = 0;
      Data7 = 0;
      TX_7_Data_Values();
      Serial.print(F("Battery Min = "));
      Serial.println(Battery_Min);
      Serial.print(F("Battery Sensitivity = "));
      Serial.println(Low_Battery_Instances_Chg);
      Serial.println(" ");
      }

// Setup Other Menu is selected on the TFT
    if (TFT_Menu_Command == 30) {
      Serial.println("TX Setup Other");
      
      Serial3.print(PCB);
      Serial3.println("\a");
      delay(300);  

      Serial.print(F("PCB = "));
      if (PCB == 1) Serial.println(F("Enabled"));
      if (PCB == 0) Serial.println(F("Disabled"));
      Serial.println(" ");
      }


// Perimeter Wire Menu is selected on the TFT
    if (TFT_Menu_Command == 6) {
      Serial.println("TX Perimeter to TFT");
      Data1 = Perimeter_Wire_Enabled;
      Data2 = WIFI_Enabled;
      Data3 = Bumper_Activate_Frnt;
      Data4 = 0;
      Data5 = 0;
      Data6 = 0;
      Data7 = 0;
      TX_7_Data_Values();
      Serial.print(F("Wire Sensor ON = "));
      Serial.println(Perimeter_Wire_Enabled);
      Serial.print(F("WIFI Enabled = "));
      Serial.println(WIFI_Enabled);
      Serial.print(F("Bumper ON = "));
      Serial.println(Bumper_Activate_Frnt);
      Serial.println(F(" "));
      }


// Rain Sensor Menu is selected on the TFT
    if (TFT_Menu_Command == 12) {
      Serial.println("TX Rain to TFT");
      Data1 = Rain_Sensor_Installed;
      Data2 = Rain_Total_Hits_Go_Home;
      Data3 = 0;
      Data4 = 0;
      Data5 = 0;
      Data6 = 0;
      Data7 = 0;
      TX_7_Data_Values();

      Serial.print(F("Rain Sensor ON = "));
      Serial.println(Rain_Sensor_Installed);
      Serial.print(F("Rain Sensitivity = "));
      Serial.println(Rain_Total_Hits_Go_Home);
      Serial.println(F(" "));
      }


// Wheel Motor Menu is selected on the TFT Screen
    if (TFT_Menu_Command == 14) {
      Serial.println("TX Wheel PWM to TFT");
      Data1 = PWM_MaxSpeed_LH;
      Data2 = PWM_MaxSpeed_RH;
      Data3 = PWM_Slow_Speed_LH;
      Data4 = PWM_Slow_Speed_RH;
      Data5 = Slow_Speed_MAG / 10;
      Data6 = 0;
      Data7 = 0;
      TX_7_Data_Values();

      Serial.print(F("PWM LH = "));
      Serial.println(PWM_MaxSpeed_LH);
      Serial.print(F("PWM RH = "));
      Serial.println(PWM_MaxSpeed_RH);
      Serial.print(F("PWM S LH = "));
      Serial.println(PWM_Slow_Speed_LH);
      Serial.print(F("PWM S RH = "));
      Serial.println(PWM_Slow_Speed_RH);
      Serial.print(F("Slow MAG = "));
      Serial.println(Slow_Speed_MAG);
      Serial.println(F(" ")); 
      }
      
      

// Blade Motor Menu is selected on the TFT Screen
    if (TFT_Menu_Command == 15) {

      Serial.println("TX Blade Data to TFT");
      Data1 = PWM_Blade_Speed;
      Data2 = Cutting_Blades_Activate;
      Data3 = 0;
      Data4 = 0;
      Data5 = 0;
      Data6 = 0;
      Data6 = 0;
      TX_7_Data_Values();
     
      Serial.print(F("Blade Motor PWM = "));
      Serial.println(PWM_Blade_Speed);
      Serial.print(F("Cutting Blade Activated = "));
      Serial.println(Cutting_Blades_Activate);
      Serial.println(F(" "));
      }


// Motion Turns Menu is selected on the TFT Screen
    if (TFT_Menu_Command == 16) {

      Serial.println("TX Turns Data to TFT");
      Data1 = Max_Cycles_Straight / 10 ;
      Data2 = Mower_Turn_Delay_Min / 100;
      Data3 = Mower_Turn_Delay_Max / 100;
      Data4 = Mower_Reverse_Delay / 100;
      Data5 = 0;
      Data6 = 0;
      Data7 = 0;
      TX_7_Data_Values();
      
      Serial.print(F("Max Mow L = "));
      Serial.println(Max_Cycles_Straight);
      Serial.print(F("Turn Min = "));
      Serial.println(Mower_Turn_Delay_Min);
      Serial.print(F("Turn Max = "));
      Serial.println(Mower_Turn_Delay_Max);
      Serial.print(F("Reverse = "));
      Serial.println(Mower_Reverse_Delay);
      Serial.println(F(" "));

}


// Tracking to Exit Menu is selected on the TFT Screen
    if (TFT_Menu_Command == 17) {
      Serial.println("TX Exit to TFT");

      Data1 = Track_Wire_Zone_1_Cycles / 100 ;
      Data2 = Track_Wire_Zone_2_Cycles / 100;
      Data3 = CCW_Tracking_To_Start;
      Data4 = 0;
      Data5 = 0;
      Data6 = 0;
      Data7 = 0;
      TX_7_Data_Values();
      Serial.print(F("Track Wire Zone 1 = "));
      Serial.println(Track_Wire_Zone_1_Cycles);    
      Serial.print(F("Track Wire Zone 2 = "));
      Serial.println(Track_Wire_Zone_2_Cycles);      
      if (CCW_Tracking_To_Start == 0) {
        CW_Tracking_To_Start = 1;
        CCW_Tracking_To_Charge = 1;
        CW_Tracking_To_Charge = 0;
        Serial.println(F("Tracking to Charge = CCW"));
        Serial.println(F("Tracking to Start = CW"));
        }        
      if (CCW_Tracking_To_Start == 1) {
        CW_Tracking_To_Start = 0;
        CCW_Tracking_To_Charge = 0;
        CW_Tracking_To_Charge = 1;        
        Serial.println(F("Tracking to Charge = CW"));
        Serial.println(F("Tracking to Start = CCW"));       
        }
    }


// Charging Options Menu is selected on the TFT Screen
    if (TFT_Menu_Command == 8) {
      Serial.println("TX Tracking to TFT");
    
      Serial3.print(Use_Charging_Station);
      Serial3.println("\a");
      delay(300); 

      Serial.print(F("Use Charging Station = "));
      Serial.println(Use_Charging_Station); 
      } 


// Find Wire Menu is selected on the TFT Screen
    if (TFT_Menu_Command == 18) {
      Serial.println("TX Find Wire to TFT");
      Data1 = Max_Cycle_Wire_Find / 100 ;
      Data2 = Max_Cycle_Wire_Find_Back / 10;
      Data3 = Home_Wire_Compass_Heading;
      Data4 = 0;
      Data5 = 0;
      Data6 = 0;
      Data7 = 0;
      TX_7_Data_Values();
      Serial.print(F("Wire Find Forwards / cylces = "));
      Serial.println(Max_Cycle_Wire_Find);      
      Serial.print(F("Wire Find Backwards / cylces = "));
      Serial.println(Max_Cycle_Wire_Find_Back);
      Serial.print(F("Home Compass Heading / degrees "));
      Serial.println(Home_Wire_Compass_Heading);      
      }

// Tracking PID Menu is selected on the TFT Screen
    if (TFT_Menu_Command == 19) {
      Serial.println("TX Find Wire to TFT");
      
      Serial3.print(Max_Tracking_Turn_Left / 10);
      Serial3.println("\a");
      delay(300);  

      Serial3.print(Max_Tracking_Turn_Right / 10);
      Serial3.println("\b");
      delay(200);  

      Serial3.print(P * 100);
      Serial3.println("\c");
      delay(200);  

      Serial.print(F("Max Cycles Left Wheel = "));
      Serial.println(Max_Tracking_Turn_Left);
      Serial.print(F("Max Cycles Right Wheel = "));
      Serial.println(Max_Tracking_Turn_Right);         
      Serial.print(F("PID P = "));
      Serial.println(P);
      Serial.println(F(" "));     
      }


// Compass Menu is selected on the TFT Screen
    if (TFT_Menu_Command == 27) {
      Serial.println("TX Compass to TFT");
      
      Serial3.print(Compass_Activate);
      Serial3.println("\a");
      delay(300);  

      Serial3.print(Compass_Heading_Hold_Enabled);
      Serial3.println("\b");
      delay(300);  

      Serial3.print(CPower * 10);
      Serial3.println("\c");
      delay(300);  
      
      Serial3.print(Compass_Setup_Mode);
      Serial3.println("\d");
      delay(200);  

      Serial.print(F("Compass Activated = "));
      Serial.println(Compass_Activate);
      Serial.print(F("Heading Hold Enabled = "));
      Serial.println(Compass_Heading_Hold_Enabled);          
      Serial.print(F("Compass Power = "));
      Serial.println(CPower);    
      Serial.print(F("Compass Setup Mode = "));
      Serial.println(Compass_Setup_Mode); 
      }


// GYRO Menu is selected on the TFT Screen
    if (TFT_Menu_Command == 28) {

      Serial3.print(GYRO_Enabled);
      Serial3.println("\a");
      delay(300);  

      Serial3.print(GPower * 10);
      Serial3.println("\b");
      delay(300);

      Serial.print(F("GYRO Enabled= "));
      Serial.println(GYRO_Enabled); 
      Serial.print(F("GYRO Power = "));
      Serial.println(GPower);     
    }


// Wheel Blockage Menu is selected on the TFT Screen
    if (TFT_Menu_Command == 29) {

      Serial.println("TX Wheel Block to TFT");
      Data1 = Wheel_Amp_Sensor_ON;
      float Temp = Max_Wheel_Amps * 10;
      int Temp2 = Temp;
      Data2 = Temp2;
      Data3 = 0;
      Data4 = 0;
      Data5 = 0;
      Data6 = 0;
      Data7 = 0;
      TX_7_Data_Values();

    Serial.print(F("Wheel Amp ON: "));
        if (Wheel_Amp_Sensor_ON == 1) Serial.println("ON");
        if (Wheel_Amp_Sensor_ON == 0) Serial.println("OFF");   
    Serial.print(F("Wheel Amps Max: "));
    Serial.print(Max_Wheel_Amps);     
    }

// Alarm 1 Menu is selected on the TFT Screen
    if (TFT_Menu_Command == 20) {
      Serial.println("TX Alarm1 TFT");

      Data1 = Alarm_1_ON;
      Data2 = Alarm_1_Hour;
      Data3 = Alarm_1_Minute;
      Data4 = Alarm_1_Repeat;
      Data5 = Alarm_1_Action;
      Data6 = 0;
      Data7 = 0;
      TX_7_Data_Values();

      Serial.print(F("Alarm 1 ON = "));
      Serial.println(Alarm_1_ON);
      Serial.print(F("Alarm 1 Time = "));
      Serial.print(Alarm_1_Hour);
      Serial.print(F(":"));
      Serial.println(Alarm_1_Minute);
      Serial.print(F("Alarm 1 Repeat = "));
      Serial.println(Alarm_1_Repeat);
      Serial.print(F("Alarm 1 Action = "));
      Serial.println(Alarm_1_Action);    
      }


// Alarm 2 Menu is selected on the TFT Screen
    if (TFT_Menu_Command == 21) {
      Serial.println("TX Alarm2 TFT");
      
      Data1 = Alarm_2_ON;
      Data2 = Alarm_2_Hour;
      Data3 = Alarm_2_Minute;
      Data4 = Alarm_2_Repeat;
      Data5 = Alarm_2_Action;
      Data6 = 0;
      Data7 = 0;
      TX_7_Data_Values();

      Serial.print(F("Alarm 2 ON = "));
      Serial.println(Alarm_2_ON);
      Serial.print(F("Alarm 2 Time = "));
      Serial.print(Alarm_2_Hour);
      Serial.print(F(":"));
      Serial.println(Alarm_2_Minute);
      Serial.print(F("Alarm 2 Repeat = "));
      Serial.println(Alarm_2_Repeat);
      Serial.print(F("Alarm 2 Action = "));
      Serial.println(Alarm_2_Action);    
      }


// Alarm 3 Menu is selected on the TFT Screen
    if (TFT_Menu_Command == 22) {
      Serial.println("TX Alarm3 TFT");
      
      Data1 = Alarm_3_ON;
      Data2 = Alarm_3_Hour;
      Data3 = Alarm_3_Minute;
      Data4 = Alarm_3_Repeat;
      Data5 = Alarm_3_Action;
      Data6 = 0;
      Data7 = 0;
      TX_7_Data_Values();

      Serial.print(F("Alarm 3 ON = "));
      Serial.println(Alarm_3_ON);
      Serial.print(F("Alarm 3 Time = "));
      Serial.print(Alarm_3_Hour);
      Serial.print(F(":"));
      Serial.println(Alarm_3_Minute);
      Serial.print(F("Alarm 3 Repeat = "));
      Serial.println(Alarm_3_Repeat);
      Serial.print(F("Alarm 3 Action = "));
      Serial.println(Alarm_3_Action);    
      }


// Set Time Menu is selected on the TFT Screen
    if (TFT_Menu_Command == 23) {
      Serial.println("Set Time TFT");
      if (PCB == 0) {
        Time t = rtc.time();
        Time_Hour = t.hr;
        Time_Minute = t.min;  
        }
      if (PCB == 1) {
        byte second, minute, hour, dayOfWeek, dayOfMonth, month, year;
        Read_DS3231_Time(&second, &minute, &hour, &dayOfWeek, &dayOfMonth, &month,
                 &year);
        Time_Hour = hour;
        Time_Minute = minute;
        Time_Second = second;
        }
 
      Serial3.print(Time_Hour);
      Serial3.println("\a");
      delay(300);  

      Serial3.print(Time_Minute);
      Serial3.println("\b");
      delay(200);  

      Serial.print(F("Time Now = "));
      Serial.print(Time_Hour);
      Serial.print(F(":"));
      Serial.println(Time_Minute);
      }



// Tip Sensor Menu is selected on the TFT Screen
    if (TFT_Menu_Command == 24) {

      Serial.println("TX Tip Sensor to TFT");
      Data1 = Angle_Sensor_Enabled;
      Data2 = Tip_Over_Sensor_Enabled;
      Data3 = 0;
      Data4 = 0;
      Data5 = 0;
      Data6 = 0;
      Data7 = 0;
      TX_7_Data_Values();
      Serial.print(F("Angle ON = "));
      Serial.println(Angle_Sensor_Enabled);
      Serial.print(F("Tip ON = "));
      Serial.println(Tip_Over_Sensor_Enabled);
      Serial.println(" ");
}


// Pattern Mow Menu is selected on the TFT Screen
    if (TFT_Menu_Command == 25) {
      Serial.println("TX Pattern to TFT");
      Data1 = Pattern_Mow;
      Data2 = Turn_90_Delay_LH / 10;
      Data3 = Turn_90_Delay_RH / 10;
      Data4 = Move_to_next_line_delay / 10;
      Data5 = Line_Length_Cycles;
      Data6 = 0;
      Data7 = 0;
      TX_7_Data_Values();
      if (Pattern_Mow == 0) Serial.println("OFF");
      if (Pattern_Mow == 1) Serial.println("Parallel");  
      if (Pattern_Mow == 3) Serial.println("Spiral"); 
      Serial.print(F("Turn 90° LH= "));
      Serial.println(Turn_90_Delay_LH);  
      Serial.print(F("Turn 90° RH= "));
      Serial.println(Turn_90_Delay_RH);      
      Serial.print(F("Distance to next row= "));
      Serial.println(Move_to_next_line_delay);      
      Serial.print(F("Row Length = "));
      Serial.println(Line_Length_Cycles);  
      Serial.println(" "); 
}
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
